TheTosters/TRNG-Ring-Oscilator/host_tools/results_90kHz.txt

Opening file: 'outputA.bin'
Loaded 8388608 samples of 2 distinct 1-bit-wide symbols

Running non-IID tests...

Running Most Common Value Estimate...
Literal MCV Estimate: mode = 4298712, p-hat = 0.51244640350341797, p_u = 0.51289094014308934
	Most Common Value Estimate = 0.963276 / 1 bit(s)

Running Entropic Statistic Estimates (bit strings only)...
Literal Collision Estimate: X-bar = 2.3815616665635146, sigma-hat = 0.48576993337007718, p = 0.74403384845214471
	Collision Test Estimate = 0.426560 / 1 bit(s)
Literal Markov Estimate: P_0 = 0.48755359649658203, P_1 = 0.51244640350341797, P_0,0 = 0.56341348616529274, P_0,1 = 0.43658651383470726, P_1,0 = 0.4153788390569082, P_1,1 = 0.5846211609430918, p_max = 1.2668170204170376e-30
	Markov Test Estimate = 0.775911 / 1 bit(s)
Literal Compression Estimate: X-bar = 4.0969888509940864, sigma-hat = 1.2383501643392119, p = 0.36698478366929632
	Compression Test Estimate = 0.241035 / 1 bit(s)

Running Tuple Estimates...
Literal t-Tuple Estimate: t = 148, p-hat_max = 0.91971073380307244, p_u = 0.91995240590938887
Literal LRS Estimate: u = 149, v = 214, p-hat = 0.87358722201162486, p_u = 0.87388276508104323
	T-Tuple Test Estimate = 0.120369 / 1 bit(s)
	LRS Test Estimate = 0.194488 / 1 bit(s)

Running Predictor Estimates...
Literal MultiMCW Prediction Estimate: N = 8388545, Pglobal' = 0.51260666561552337 (C = 4296295) Plocal = 0.71283473804017683 (r = 57)
	Multi Most Common in Window (MultiMCW) Prediction Test Estimate = 0.488360 / 1 bit(s)
Literal Lag Prediction Estimate: N = 8388607, Pglobal' = 0.57471232292201824 (C = 4817347) Plocal = 0.91959446713649384 (r = 215)
	Lag Prediction Test Estimate = 0.120930 / 1 bit(s)
Literal MultiMMC Prediction Estimate: N = 8388606, Pglobal' = 0.8222529756850907 (C = 6894702) Plocal = 0.91997141567862839 (r = 216)
	Multi Markov Model with Counting (MultiMMC) Prediction Test Estimate = 0.120339 / 1 bit(s)
Literal LZ78Y Prediction Estimate: N = 8388591, Pglobal' = 0.57471866305392549 (C = 4817391) Plocal = 0.91997142372295304 (r = 216)
	LZ78Y Prediction Test Estimate = 0.120339 / 1 bit(s)

H_original: 0.120339
Opening file: 'outputB.bin'
Loaded 8388608 samples of 2 distinct 1-bit-wide symbols

Running non-IID tests...

Running Most Common Value Estimate...
Literal MCV Estimate: mode = 4230372, p-hat = 0.50429964065551758, p_u = 0.50474429864658732
	Most Common Value Estimate = 0.986375 / 1 bit(s)

Running Entropic Statistic Estimates (bit strings only)...
Literal Collision Estimate: X-bar = 2.173933144739038, sigma-hat = 0.3790520322270397, p = 0.90408161203077464
	Collision Test Estimate = 0.145475 / 1 bit(s)
Literal Markov Estimate: P_0 = 0.49570035934448242, P_1 = 0.50429964065551758, P_0,0 = 0.8178407863334356, P_0,1 = 0.1821592136665644, P_1,0 = 0.17905309014268489, P_1,1 = 0.82094690985731511, p_max = 6.617635792806642e-12
	Markov Test Estimate = 0.290131 / 1 bit(s)
Literal Compression Estimate: X-bar = 3.4138333141020731, sigma-hat = 1.375676444584367, p = 0.50823522161718859
	Compression Test Estimate = 0.162739 / 1 bit(s)

Running Tuple Estimates...
Literal t-Tuple Estimate: t = 150, p-hat_max = 0.92248832676736736, p_u = 0.92272614007370446
Literal LRS Estimate: u = 151, v = 187, p-hat = 0.85635492738619756, p_u = 0.85666684824822803
	T-Tuple Test Estimate = 0.116026 / 1 bit(s)
	LRS Test Estimate = 0.223194 / 1 bit(s)

Running Predictor Estimates...
Literal MultiMCW Prediction Estimate: N = 8388545, Pglobal' = 0.51750655364266596 (C = 4337399) Plocal = 0.8975639045458621 (r = 169)
	Multi Most Common in Window (MultiMCW) Prediction Test Estimate = 0.155913 / 1 bit(s)
Literal Lag Prediction Estimate: N = 8388607, Pglobal' = 0.81974931825735786 (C = 6873685) Plocal = 0.89695502392683157 (r = 168)
	Lag Prediction Test Estimate = 0.156892 / 1 bit(s)
Literal MultiMMC Prediction Estimate: N = 8388606, Pglobal' = 0.83215606509176343 (C = 6977839) Plocal = 0.89695502459785259 (r = 168)
	Multi Markov Model with Counting (MultiMMC) Prediction Test Estimate = 0.156892 / 1 bit(s)
Literal LZ78Y Prediction Estimate: N = 8388591, Pglobal' = 0.81974945086986895 (C = 6873673) Plocal = 0.89695503466686577 (r = 168)
	LZ78Y Prediction Test Estimate = 0.156892 / 1 bit(s)

H_original: 0.116026
Opening file: 'outputC.bin'
Loaded 8388608 samples of 2 distinct 1-bit-wide symbols

Running non-IID tests...

Running Most Common Value Estimate...
Literal MCV Estimate: mode = 4272873, p-hat = 0.50936615467071533, p_u = 0.50981075107855722
	Most Common Value Estimate = 0.971966 / 1 bit(s)

Running Entropic Statistic Estimates (bit strings only)...
Literal Collision Estimate: X-bar = 2.4836991649062239, sigma-hat = 0.49973428611273651, p = 0.59219885774090075
	Collision Test Estimate = 0.755846 / 1 bit(s)
Literal Markov Estimate: P_0 = 0.49063384532928467, P_1 = 0.50936615467071533, P_0,0 = 0.44018345208898341, P_0,1 = 0.55981654791101665, P_1,0 = 0.53922899182821493, P_1,1 = 0.46077100817178507, p_max = 4.6494135477684564e-34
	Markov Test Estimate = 0.865066 / 1 bit(s)
Literal Compression Estimate: X-bar = 4.1554362921222205, sigma-hat = 1.2654374991161359, p = 0.35391090490677524
	Compression Test Estimate = 0.249757 / 1 bit(s)

Running Tuple Estimates...
Literal t-Tuple Estimate: t = 82, p-hat_max = 0.86038147790838959, p_u = 0.86068971805304306
Literal LRS Estimate: u = 83, v = 119, p-hat = 0.77715304576111677, p_u = 0.77752315402597705
	T-Tuple Test Estimate = 0.216435 / 1 bit(s)
	LRS Test Estimate = 0.363042 / 1 bit(s)

Running Predictor Estimates...
Literal MultiMCW Prediction Estimate: N = 8388545, Pglobal' = 0.50922604696704044 (C = 4267936) Plocal can't affect result (r = 13)
	Multi Most Common in Window (MultiMCW) Prediction Test Estimate = 0.973622 / 1 bit(s)
Literal Lag Prediction Estimate: N = 8388607, Pglobal' = 0.58395104214111504 (C = 4894858) Plocal = 0.83661674891755911 (r = 105)
	Lag Prediction Test Estimate = 0.257361 / 1 bit(s)
Literal MultiMMC Prediction Estimate: N = 8388606, Pglobal' = 0.82287085094884427 (C = 6899889) Plocal = 0.83955329877997165 (r = 107)
	Multi Markov Model with Counting (MultiMMC) Prediction Test Estimate = 0.252306 / 1 bit(s)
Literal LZ78Y Prediction Estimate: N = 8388591, Pglobal' = 0.54976741631726744 (C = 4608062) Plocal can't affect result (r = 16)
	LZ78Y Prediction Test Estimate = 0.863107 / 1 bit(s)

H_original: 0.216435
Opening file: 'outputD.bin'
Loaded 8388608 samples of 2 distinct 1-bit-wide symbols

Running non-IID tests...

Running Most Common Value Estimate...
Literal MCV Estimate: mode = 4335821, p-hat = 0.51687014102935791, p_u = 0.51731456227980532
	Most Common Value Estimate = 0.950886 / 1 bit(s)

Running Entropic Statistic Estimates (bit strings only)...
Literal Collision Estimate: X-bar = 2.2929617626863648, sigma-hat = 0.45512111015518786, p = 0.82221976076494396
	Collision Test Estimate = 0.282404 / 1 bit(s)
Literal Markov Estimate: P_0 = 0.48312985897064209, P_1 = 0.51687014102935791, P_0,0 = 0.71552235918698892, P_0,1 = 0.28447764081301108, P_1,0 = 0.26590765624318902, P_1,1 = 0.73409234375681098, p_max = 4.6101988602429338e-18
	Markov Test Estimate = 0.449921 / 1 bit(s)
Literal Compression Estimate: X-bar = 4.0684669349208216, sigma-hat = 1.1736546335303886, p = 0.37327169556855921
	Compression Test Estimate = 0.236950 / 1 bit(s)

Running Tuple Estimates...
Literal t-Tuple Estimate: t = 91, p-hat_max = 0.87300709263041121, p_u = 0.87330321469890448
Literal LRS Estimate: u = 92, v = 111, p-hat = 0.77085064704799344, p_u = 0.77122442750751286
	T-Tuple Test Estimate = 0.195445 / 1 bit(s)
	LRS Test Estimate = 0.374777 / 1 bit(s)

Running Predictor Estimates...
Literal MultiMCW Prediction Estimate: N = 8388545, Pglobal' = 0.51703962133377257 (C = 4333482) Plocal = 0.8366168108271288 (r = 105)
	Multi Most Common in Window (MultiMCW) Prediction Test Estimate = 0.257361 / 1 bit(s)
Literal Lag Prediction Estimate: N = 8388607, Pglobal' = 0.72551768378603787 (C = 6082752) Plocal = 0.84646646661947711 (r = 112)
	Lag Prediction Test Estimate = 0.240475 / 1 bit(s)
Literal MultiMMC Prediction Estimate: N = 8388606, Pglobal' = 0.80895859134096559 (C = 6783100) Plocal = 0.83042085935645926 (r = 101)
	Multi Markov Model with Counting (MultiMMC) Prediction Test Estimate = 0.268085 / 1 bit(s)
Literal LZ78Y Prediction Estimate: N = 8388591, Pglobal' = 0.72551751757617944 (C = 6082739) Plocal = 0.84646648178079575 (r = 112)
	LZ78Y Prediction Test Estimate = 0.240475 / 1 bit(s)

H_original: 0.195445
Opening file: 'outputE.bin'
Loaded 8388608 samples of 2 distinct 1-bit-wide symbols

Running non-IID tests...

Running Most Common Value Estimate...
Literal MCV Estimate: mode = 4305989, p-hat = 0.513313889503479, p_u = 0.51375840626253888
	Most Common Value Estimate = 0.960838 / 1 bit(s)

Running Entropic Statistic Estimates (bit strings only)...
Literal Collision Estimate: X-bar = 2.609804851247532, sigma-hat = 0.48779398178909766, p = 0.5
	Collision Test Estimate = 1.000000 / 1 bit(s)
Literal Markov Estimate: P_0 = 0.486686110496521, P_1 = 0.513313889503479, P_0,0 = 0.35408039645149264, P_0,1 = 0.6459196035485073, P_1,0 = 0.61241308326612076, P_1,1 = 0.38758691673387924, p_max = 1.3257810065688544e-26
	Markov Test Estimate = 0.671588 / 1 bit(s)
Literal Compression Estimate: X-bar = 4.1545489860127169, sigma-hat = 1.2084756619072359, p = 0.35408303695351973
	Compression Test Estimate = 0.249640 / 1 bit(s)

Running Tuple Estimates...
Literal t-Tuple Estimate: t = 76, p-hat_max = 0.85022349373191985, p_u = 0.85054085984579109
Literal LRS Estimate: u = 77, v = 108, p-hat = 0.75469758505810292, p_u = 0.75508024195678169
	T-Tuple Test Estimate = 0.233548 / 1 bit(s)
	LRS Test Estimate = 0.405298 / 1 bit(s)

Running Predictor Estimates...
Literal MultiMCW Prediction Estimate: N = 8388545, Pglobal' = 0.513408813018286 (C = 4303024) Plocal can't affect result (r = 12)
	Multi Most Common in Window (MultiMCW) Prediction Test Estimate = 0.961820 / 1 bit(s)
Literal Lag Prediction Estimate: N = 8388607, Pglobal' = 0.62968135364052824 (C = 5278546) Plocal = 0.70371374522201624 (r = 55)
	Lag Prediction Test Estimate = 0.506939 / 1 bit(s)
Literal MultiMMC Prediction Estimate: N = 8388606, Pglobal' = 0.81340886948187918 (C = 6820458) Plocal = 0.83809789327235407 (r = 106)
	Multi Markov Model with Counting (MultiMMC) Prediction Test Estimate = 0.254809 / 1 bit(s)
Literal LZ78Y Prediction Estimate: N = 8388591, Pglobal' = 0.62914945635925423 (C = 5274073) Plocal = 0.80251477315347142 (r = 86)
	LZ78Y Prediction Test Estimate = 0.317400 / 1 bit(s)

H_original: 0.233548
Opening file: 'outputF.bin'
Loaded 8388608 samples of 2 distinct 1-bit-wide symbols

Running non-IID tests...

Running Most Common Value Estimate...
Literal MCV Estimate: mode = 4260564, p-hat = 0.50789880752563477, p_u = 0.50834342646735065
	Most Common Value Estimate = 0.976125 / 1 bit(s)

Running Entropic Statistic Estimates (bit strings only)...
Literal Collision Estimate: X-bar = 2.7115709227400528, sigma-hat = 0.45303179909682284, p = 0.5
	Collision Test Estimate = 1.000000 / 1 bit(s)
Literal Markov Estimate: P_0 = 0.49210119247436523, P_1 = 0.50789880752563477, P_0,0 = 0.2674266553360381, P_0,1 = 0.73257334466396196, P_1,0 = 0.70978765012980682, P_1,1 = 0.29021234987019318, p_max = 4.6091129125894903e-19
	Markov Test Estimate = 0.475876 / 1 bit(s)
Literal Compression Estimate: X-bar = 3.9043233688137411, sigma-hat = 1.2903146020321519, p = 0.40887981166314613
	Compression Test Estimate = 0.215042 / 1 bit(s)

Running Tuple Estimates...
Literal t-Tuple Estimate: t = 138, p-hat_max = 0.91414962264868693, p_u = 0.91439876749138815
Literal LRS Estimate: u = 139, v = 173, p-hat = 0.84102190629608664, p_u = 0.84134710173967131
	T-Tuple Test Estimate = 0.129105 / 1 bit(s)
	LRS Test Estimate = 0.249227 / 1 bit(s)

Running Predictor Estimates...
Literal MultiMCW Prediction Estimate: N = 8388545, Pglobal' = 0.50708398853688175 (C = 4249967) Plocal can't affect result (r = 13)
	Multi Most Common in Window (MultiMCW) Prediction Test Estimate = 0.979703 / 1 bit(s)
Literal Lag Prediction Estimate: N = 8388607, Pglobal' = 0.53158253313116521 (C = 4455514) Plocal = 0.80464711951090206 (r = 87)
	Lag Prediction Test Estimate = 0.313572 / 1 bit(s)
Literal MultiMMC Prediction Estimate: N = 8388606, Pglobal' = 0.80132154710984138 (C = 6718992) Plocal = 0.89380262309515446 (r = 163)
	Multi Markov Model with Counting (MultiMMC) Prediction Test Estimate = 0.161972 / 1 bit(s)
Literal LZ78Y Prediction Estimate: N = 8388591, Pglobal' = 0.72139886683620547 (C = 6048174) Plocal = 0.89181998752301628 (r = 160)
	LZ78Y Prediction Test Estimate = 0.165176 / 1 bit(s)

H_original: 0.129105
Opening file: 'outputA-F.bin'
Loaded 1398101 samples of 64 distinct 6-bit-wide symbols
Number of Binary Symbols: 8388606

Running non-IID tests...

Running Most Common Value Estimate...
Bitstring MCV Estimate: mode = 4279520, p-hat = 0.51015866044966229, p_u = 0.51060324314650907
	Most Common Value Estimate (bit string) = 0.969725 / 1 bit(s)
Literal MCV Estimate: mode = 30234, p-hat = 0.021625047117482928, p_u = 0.021941915681613411
	Most Common Value Estimate = 5.510167 / 6 bit(s)

Running Entropic Statistic Estimates (bit strings only)...
Bitstring Collision Estimate: X-bar = 2.4942242713215821, sigma-hat = 0.49996671417409239, p = 0.55691204344919609
	Collision Test Estimate (bit string) = 0.844479 / 1 bit(s)
Bitstring Markov Estimate: P_0 = 0.48984133955033771, P_1 = 0.51015866044966229, P_0,0 = 0.49528520339686327, P_0,1 = 0.50471479660313667, P_1,0 = 0.48461439600702882, P_1,1 = 0.51538560399297118, p_max = 1.4076842853261408e-37
	Markov Test Estimate (bit string) = 0.956391 / 1 bit(s)
Bitstring Compression Estimate: X-bar = 5.1839970913330653, sigma-hat = 1.0208165534184075, p = 0.05185236007780869
	Compression Test Estimate (bit string) = 0.711574 / 1 bit(s)

Running Tuple Estimates...
Bitstring t-Tuple Estimate: t = 28, p-hat_max = 0.6492966990368092, p_u = 0.64972108765842607
Bitstring LRS Estimate: u = 29, v = 90, p-hat = 0.71451064879251669, p_u = 0.71491232075373568
	T-Tuple Test Estimate (bit string) = 0.622108 / 1 bit(s)
Literal t-Tuple Estimate: t = 4, p-hat_max = 0.08288989323938957, p_u = 0.083490526657149858
Literal LRS Estimate: u = 5, v = 14, p-hat = 0.14624155830546209, p_u = 0.14701131038388546
	T-Tuple Test Estimate = 3.582244 / 6 bit(s)
	LRS Test Estimate (bit string) = 0.484162 / 1 bit(s)
	LRS Test Estimate = 2.766001 / 6 bit(s)

Running Predictor Estimates...
Bitstring MultiMCW Prediction Estimate: N = 8388543, Pglobal' = 0.50994773600696053 (C = 4273989) Plocal can't affect result (r = 19)
	Multi Most Common in Window (MultiMCW) Prediction Test Estimate (bit string) = 0.971579 / 1 bit(s)
Literal MultiMCW Prediction Estimate: N = 1398038, Pglobal' = 0.020720229688916007 (C = 28537) Plocal can't affect result (r = 4)
	Multi Most Common in Window (MultiMCW) Prediction Test Estimate = 5.592816 / 6 bit(s)
Bitstring Lag Prediction Estimate: N = 8388605, Pglobal' = 0.53051782092749111 (C = 4446581) Plocal can't affect result (r = 23)
	Lag Prediction Test Estimate (bit string) = 0.914527 / 1 bit(s)
Literal Lag Prediction Estimate: N = 1398100, Pglobal' = 0.024532587396390054 (C = 33831) Plocal can't affect result (r = 5)
	Lag Prediction Test Estimate = 5.349157 / 6 bit(s)
Bitstring MultiMMC Prediction Estimate: N = 8388604, Pglobal' = 0.61223139835262042 (C = 5132131) Plocal can't affect result (r = 34)
	Multi Markov Model with Counting (MultiMMC) Prediction Test Estimate (bit string) = 0.707851 / 1 bit(s)
Literal MultiMMC Prediction Estimate: N = 1398099, Pglobal' = 0.11453364169286714 (C = 159162) Plocal can't affect result (r = 8)
	Multi Markov Model with Counting (MultiMMC) Prediction Test Estimate = 3.126157 / 6 bit(s)
Bitstring LZ78Y Prediction Estimate: N = 8388589, Pglobal' = 0.51056958809083852 (C = 4279229) Plocal can't affect result (r = 19)
	LZ78Y Prediction Test Estimate (bit string) = 0.969820 / 1 bit(s)
Literal LZ78Y Prediction Estimate: N = 1398084, Pglobal' = 0.054053795111667954 (C = 74886) Plocal can't affect result (r = 4)
	LZ78Y Prediction Test Estimate = 4.209460 / 6 bit(s)

H_original: 2.766001
H_bitstring: 0.484162
min(H_original, 6 X H_bitstring): 2.766001
