TheTosters/TRNG-Ring-Oscilator/host_tools/Rev_2/sweep/300kHz/results.txt

########## channel A (1 bit/sample, little) ##########
Opening file: 'Rev_2/sweep/300kHz/outputA.bin'
Loaded 4194304 samples of 2 distinct 1-bit-wide symbols

Running non-IID tests...

Running Most Common Value Estimate...
Literal MCV Estimate: mode = 2104973, p-hat = 0.50186467170715332, p_u = 0.50249353198504088
	Most Common Value Estimate = 0.992823 / 1 bit(s)

Running Entropic Statistic Estimates (bit strings only)...
Literal Collision Estimate: X-bar = 2.4009455401393751, sigma-hat = 0.49009014627186415, p = 0.72361749916627005
	Collision Test Estimate = 0.466701 / 1 bit(s)
Literal Markov Estimate: P_0 = 0.49813532829284668, P_1 = 0.50186467170715332, P_0,0 = 0.58695945590213128, P_0,1 = 0.41304054409786872, P_1,0 = 0.40997105426055347, P_1,1 = 0.59002894573944653, p_max = 3.9948271499480619e-30
	Markov Test Estimate = 0.762966 / 1 bit(s)
Literal Compression Estimate: X-bar = 4.8000140811946661, sigma-hat = 1.1849010690096364, p = 0.19228632566695947
	Compression Test Estimate = 0.396445 / 1 bit(s)

Running Tuple Estimates...
Literal t-Tuple Estimate: t = 35, p-hat_max = 0.71711203262643819, p_u = 0.71767851698317953
Literal LRS Estimate: u = 36, v = 52, p-hat = 0.57241842177660929, p_u = 0.57304065539682425
	T-Tuple Test Estimate = 0.478590 / 1 bit(s)
	LRS Test Estimate = 0.803291 / 1 bit(s)

Running Predictor Estimates...
Literal MultiMCW Prediction Estimate: N = 4194241, Pglobal' = 0.49990346928946011 (C = 2094078) Plocal = 0.68272672936166467 (r = 49)
	Multi Most Common in Window (MultiMCW) Prediction Test Estimate = 0.550620 / 1 bit(s)
Literal Lag Prediction Estimate: N = 4194303, Pglobal' = 0.58911862191860864 (C = 2468346) Plocal = 0.67707018882865655 (r = 48)
	Lag Prediction Test Estimate = 0.562623 / 1 bit(s)
Literal MultiMMC Prediction Estimate: N = 4194302, Pglobal' = 0.63641327884093557 (C = 2666771) Plocal = 0.67707019234508858 (r = 48)
	Multi Markov Model with Counting (MultiMMC) Prediction Test Estimate = 0.562623 / 1 bit(s)
Literal LZ78Y Prediction Estimate: N = 4194287, Pglobal' = 0.58911824552680403 (C = 2468335) Plocal = 0.67707024509547686 (r = 48)
	LZ78Y Prediction Test Estimate = 0.562623 / 1 bit(s)

H_original: 0.396445

########## channel B (1 bit/sample, little) ##########
Opening file: 'Rev_2/sweep/300kHz/outputB.bin'
Loaded 4194304 samples of 2 distinct 1-bit-wide symbols

Running non-IID tests...

Running Most Common Value Estimate...
Literal MCV Estimate: mode = 2149442, p-hat = 0.5124669075012207, p_u = 0.5130955766408114
	Most Common Value Estimate = 0.962701 / 1 bit(s)

Running Entropic Statistic Estimates (bit strings only)...
Literal Collision Estimate: X-bar = 2.3396478063621107, sigma-hat = 0.47358980046711291, p = 0.78395711907345444
	Collision Test Estimate = 0.351153 / 1 bit(s)
Literal Markov Estimate: P_0 = 0.4875330924987793, P_1 = 0.5124669075012207, P_0,0 = 0.65388014148638951, P_0,1 = 0.34611985851361049, P_1,0 = 0.32927941298253222, P_1,1 = 0.67072058701746773, p_max = 4.7913035985386578e-23
	Markov Test Estimate = 0.579249 / 1 bit(s)
Literal Compression Estimate: X-bar = 4.7130704313544349, sigma-hat = 1.2276205430137941, p = 0.21676812413000471
	Compression Test Estimate = 0.367629 / 1 bit(s)

Running Tuple Estimates...
Literal t-Tuple Estimate: t = 44, p-hat_max = 0.7675842442246763, p_u = 0.76811547470794417
Literal LRS Estimate: u = 45, v = 63, p-hat = 0.63119868239556165, p_u = 0.63180551157100495
	T-Tuple Test Estimate = 0.380605 / 1 bit(s)
	LRS Test Estimate = 0.662448 / 1 bit(s)

Running Predictor Estimates...
Literal MultiMCW Prediction Estimate: N = 4194241, Pglobal' = 0.51098328971911711 (C = 2140550) Plocal = 0.7083906066829706 (r = 54)
	Multi Most Common in Window (MultiMCW) Prediction Test Estimate = 0.497383 / 1 bit(s)
Literal Lag Prediction Estimate: N = 4194303, Pglobal' = 0.66310455968221371 (C = 2778767) Plocal = 0.74208279285977319 (r = 62)
	Lag Prediction Test Estimate = 0.430348 / 1 bit(s)
Literal MultiMMC Prediction Estimate: N = 4194302, Pglobal' = 0.66374912249817097 (C = 2781471) Plocal = 0.7420827958526679 (r = 62)
	Multi Markov Model with Counting (MultiMMC) Prediction Test Estimate = 0.430348 / 1 bit(s)
Literal LZ78Y Prediction Estimate: N = 4194287, Pglobal' = 0.66310446552747671 (C = 2778756) Plocal = 0.74208284074089403 (r = 62)
	LZ78Y Prediction Test Estimate = 0.430348 / 1 bit(s)

H_original: 0.351153

########## channel C (1 bit/sample, little) ##########
Opening file: 'Rev_2/sweep/300kHz/outputC.bin'
Loaded 4194304 samples of 2 distinct 1-bit-wide symbols

Running non-IID tests...

Running Most Common Value Estimate...
Literal MCV Estimate: mode = 2135096, p-hat = 0.50904655456542969, p_u = 0.5096753162752784
	Most Common Value Estimate = 0.972350 / 1 bit(s)

Running Entropic Statistic Estimates (bit strings only)...
Literal Collision Estimate: X-bar = 2.5236926516768343, sigma-hat = 0.4994384930526059, p = 0.5
	Collision Test Estimate = 1.000000 / 1 bit(s)
Literal Markov Estimate: P_0 = 0.49095344543457031, P_1 = 0.50904655456542969, P_0,0 = 0.45386063664313497, P_0,1 = 0.54613936335686497, P_1,0 = 0.52672760381734596, P_1,1 = 0.47327239618265404, p_max = 2.179646039319764e-35
	Markov Test Estimate = 0.899558 / 1 bit(s)
Literal Compression Estimate: X-bar = 4.834841144327866, sigma-hat = 1.1700264995820584, p = 0.18211362950822052
	Compression Test Estimate = 0.409515 / 1 bit(s)

Running Tuple Estimates...
Literal t-Tuple Estimate: t = 30, p-hat_max = 0.67783114505111675, p_u = 0.67841889109665721
Literal LRS Estimate: u = 31, v = 50, p-hat = 0.56261013677922722, p_u = 0.56323405161454465
	T-Tuple Test Estimate = 0.559752 / 1 bit(s)
	LRS Test Estimate = 0.828194 / 1 bit(s)

Running Predictor Estimates...
Literal MultiMCW Prediction Estimate: N = 4194241, Pglobal' = 0.50752195189640548 (C = 2126032) Plocal = 0.59945055608291298 (r = 37)
	Multi Most Common in Window (MultiMCW) Prediction Test Estimate = 0.738287 / 1 bit(s)
Literal Lag Prediction Estimate: N = 4194303, Pglobal' = 0.51779332453569549 (C = 2169146) Plocal = 0.65889174011725271 (r = 45)
	Lag Prediction Test Estimate = 0.601887 / 1 bit(s)
Literal MultiMMC Prediction Estimate: N = 4194302, Pglobal' = 0.63116107227105633 (C = 2644734) Plocal = 0.67707019234508858 (r = 48)
	Multi Markov Model with Counting (MultiMMC) Prediction Test Estimate = 0.562623 / 1 bit(s)
Literal LZ78Y Prediction Estimate: N = 4194287, Pglobal' = 0.53687568437009525 (C = 2249180) Plocal = 0.67707024509547686 (r = 48)
	LZ78Y Prediction Test Estimate = 0.562623 / 1 bit(s)

H_original: 0.409515

########## channel D (1 bit/sample, little) ##########
Opening file: 'Rev_2/sweep/300kHz/outputD.bin'
Loaded 4194304 samples of 2 distinct 1-bit-wide symbols

Running non-IID tests...

Running Most Common Value Estimate...
Literal MCV Estimate: mode = 2140860, p-hat = 0.51042079925537109, p_u = 0.51104952731089448
	Most Common Value Estimate = 0.968465 / 1 bit(s)

Running Entropic Statistic Estimates (bit strings only)...
Literal Collision Estimate: X-bar = 2.6637943298445279, sigma-hat = 0.47241037165435557, p = 0.5
	Collision Test Estimate = 1.000000 / 1 bit(s)
Literal Markov Estimate: P_0 = 0.48957920074462891, P_1 = 0.51042079925537109, P_0,0 = 0.32409405856697332, P_0,1 = 0.67590594143302662, P_1,0 = 0.6483070580547341, P_1,1 = 0.3516929419452659, p_max = 8.8050351173577593e-24
	Markov Test Estimate = 0.598343 / 1 bit(s)
Literal Compression Estimate: X-bar = 4.7414444428009972, sigma-hat = 1.2232078300470093, p = 0.20891815025471139
	Compression Test Estimate = 0.376498 / 1 bit(s)

Running Tuple Estimates...
Literal t-Tuple Estimate: t = 36, p-hat_max = 0.72545950049844177, p_u = 0.72602080299653482
Literal LRS Estimate: u = 37, v = 56, p-hat = 0.60601644543564825, p_u = 0.60663101129574781
	T-Tuple Test Estimate = 0.461917 / 1 bit(s)
	LRS Test Estimate = 0.721109 / 1 bit(s)

Running Predictor Estimates...
Literal MultiMCW Prediction Estimate: N = 4194241, Pglobal' = 0.5092924402117176 (C = 2133458) Plocal can't affect result (r = 17)
	Multi Most Common in Window (MultiMCW) Prediction Test Estimate = 0.973434 / 1 bit(s)
Literal Lag Prediction Estimate: N = 4194303, Pglobal' = 0.57999534157353749 (C = 2430072) Plocal = 0.7219652006235483 (r = 57)
	Lag Prediction Test Estimate = 0.469999 / 1 bit(s)
Literal MultiMMC Prediction Estimate: N = 4194302, Pglobal' = 0.66251655413784383 (C = 2776299) Plocal = 0.72622510066901247 (r = 58)
	Multi Markov Model with Counting (MultiMMC) Prediction Test Estimate = 0.461511 / 1 bit(s)
Literal LZ78Y Prediction Estimate: N = 4194287, Pglobal' = 0.66241287036999663 (C = 2775854) Plocal = 0.72622514759518997 (r = 58)
	LZ78Y Prediction Test Estimate = 0.461511 / 1 bit(s)

H_original: 0.376498

########## channel E (1 bit/sample, little) ##########
Opening file: 'Rev_2/sweep/300kHz/outputE.bin'
Loaded 4194304 samples of 2 distinct 1-bit-wide symbols

Running non-IID tests...

Running Most Common Value Estimate...
Literal MCV Estimate: mode = 2110117, p-hat = 0.50309109687805176, p_u = 0.50371994951151278
	Most Common Value Estimate = 0.989306 / 1 bit(s)

Running Entropic Statistic Estimates (bit strings only)...
Literal Collision Estimate: X-bar = 2.3443902204539651, sigma-hat = 0.47516915168358986, p = 0.77975421454803273
	Collision Test Estimate = 0.358909 / 1 bit(s)
Literal Markov Estimate: P_0 = 0.49690890312194824, P_1 = 0.50309109687805176, P_0,0 = 0.65248063272663759, P_0,1 = 0.34751936727336241, P_1,0 = 0.34324921319528728, P_1,1 = 0.65675078680471266, p_max = 3.2473048007993448e-24
	Markov Test Estimate = 0.609586 / 1 bit(s)
Literal Compression Estimate: X-bar = 4.7018737406979012, sigma-hat = 1.2244399261081302, p = 0.21982968148533172
	Compression Test Estimate = 0.364257 / 1 bit(s)

Running Tuple Estimates...
Literal t-Tuple Estimate: t = 44, p-hat_max = 0.76850316884669401, p_u = 0.76903366536218165
Literal LRS Estimate: u = 45, v = 63, p-hat = 0.63423235845356107, p_u = 0.63483813718023108
	T-Tuple Test Estimate = 0.378881 / 1 bit(s)
	LRS Test Estimate = 0.655539 / 1 bit(s)

Running Predictor Estimates...
Literal MultiMCW Prediction Estimate: N = 4194241, Pglobal' = 0.50583084924175137 (C = 2118939) Plocal = 0.73438064201989661 (r = 60)
	Multi Most Common in Window (MultiMCW) Prediction Test Estimate = 0.445400 / 1 bit(s)
Literal Lag Prediction Estimate: N = 4194303, Pglobal' = 0.6552259931197274 (C = 2745708) Plocal = 0.74936803417853515 (r = 64)
	Lag Prediction Test Estimate = 0.416254 / 1 bit(s)
Literal MultiMMC Prediction Estimate: N = 4194302, Pglobal' = 0.65917772972033162 (C = 2762289) Plocal = 0.74936803710731892 (r = 64)
	Multi Markov Model with Counting (MultiMMC) Prediction Test Estimate = 0.416254 / 1 bit(s)
Literal LZ78Y Prediction Estimate: N = 4194287, Pglobal' = 0.65522729884645348 (C = 2745703) Plocal = 0.74936808103399155 (r = 64)
	LZ78Y Prediction Test Estimate = 0.416254 / 1 bit(s)

H_original: 0.358909

########## channel F (1 bit/sample, little) ##########
Opening file: 'Rev_2/sweep/300kHz/outputF.bin'
Loaded 4194304 samples of 2 distinct 1-bit-wide symbols

Running non-IID tests...

Running Most Common Value Estimate...
Literal MCV Estimate: mode = 2186627, p-hat = 0.5213325023651123, p_u = 0.52196079439344656
	Most Common Value Estimate = 0.937987 / 1 bit(s)

Running Entropic Statistic Estimates (bit strings only)...
Literal Collision Estimate: X-bar = 2.6755490092763528, sigma-hat = 0.46816950472973917, p = 0.5
	Collision Test Estimate = 1.000000 / 1 bit(s)
Literal Markov Estimate: P_0 = 0.4786674976348877, P_1 = 0.5213325023651123, P_0,0 = 0.29387909204473234, P_0,1 = 0.70612090795526772, P_1,0 = 0.64833279750044248, P_1,1 = 0.35166720249955752, p_max = 1.417646590214333e-22
	Markov Test Estimate = 0.567023 / 1 bit(s)
Literal Compression Estimate: X-bar = 4.6660745243763895, sigma-hat = 1.2510538149355399, p = 0.22953504411320583
	Compression Test Estimate = 0.353869 / 1 bit(s)

Running Tuple Estimates...
Literal t-Tuple Estimate: t = 41, p-hat_max = 0.75430405880002771, p_u = 0.75484551008962619
Literal LRS Estimate: u = 42, v = 58, p-hat = 0.61684472876018948, p_u = 0.61745618095793209
	T-Tuple Test Estimate = 0.405747 / 1 bit(s)
	LRS Test Estimate = 0.695591 / 1 bit(s)

Running Predictor Estimates...
Literal MultiMCW Prediction Estimate: N = 4194241, Pglobal' = 0.52144532054805992 (C = 2184432) Plocal can't affect result (r = 18)
	Multi Most Common in Window (MultiMCW) Prediction Test Estimate = 0.939412 / 1 bit(s)
Literal Lag Prediction Estimate: N = 4194303, Pglobal' = 0.60452167273537072 (C = 2532967) Plocal = 0.72622509754087183 (r = 58)
	Lag Prediction Test Estimate = 0.461511 / 1 bit(s)
Literal MultiMMC Prediction Estimate: N = 4194302, Pglobal' = 0.67658214697122576 (C = 2835321) Plocal = 0.73036180461747902 (r = 59)
	Multi Markov Model with Counting (MultiMMC) Prediction Test Estimate = 0.453317 / 1 bit(s)
Literal LZ78Y Prediction Estimate: N = 4194287, Pglobal' = 0.67658170475001456 (C = 2835309) Plocal = 0.73036185101896012 (r = 59)
	LZ78Y Prediction Test Estimate = 0.453317 / 1 bit(s)

H_original: 0.353869

########## channel G (1 bit/sample, little) ##########
Opening file: 'Rev_2/sweep/300kHz/outputG.bin'
Loaded 4194304 samples of 2 distinct 1-bit-wide symbols

Running non-IID tests...

Running Most Common Value Estimate...
Literal MCV Estimate: mode = 2146213, p-hat = 0.51169705390930176, p_u = 0.51232574645290985
	Most Common Value Estimate = 0.964867 / 1 bit(s)

Running Entropic Statistic Estimates (bit strings only)...
Literal Collision Estimate: X-bar = 2.4063907606778026, sigma-hat = 0.49115929057516139, p = 0.71744829241707075
	Collision Test Estimate = 0.479053 / 1 bit(s)
Literal Markov Estimate: P_0 = 0.48830294609069824, P_1 = 0.51169705390930176, P_0,0 = 0.58122641094873762, P_0,1 = 0.41877358905126238, P_1,0 = 0.399628089103924, P_1,1 = 0.600371910896076, p_max = 3.7016834769443604e-29
	Markov Test Estimate = 0.737873 / 1 bit(s)
Literal Compression Estimate: X-bar = 4.8643878273632941, sigma-hat = 1.1647840650344596, p = 0.17329691617628465
	Compression Test Estimate = 0.421447 / 1 bit(s)

Running Tuple Estimates...
Literal t-Tuple Estimate: t = 30, p-hat_max = 0.68339222106976472, p_u = 0.68397725760055172
Literal LRS Estimate: u = 31, v = 51, p-hat = 0.56897581795384833, p_u = 0.56959867000881403
	T-Tuple Test Estimate = 0.547980 / 1 bit(s)
	LRS Test Estimate = 0.811982 / 1 bit(s)

Running Predictor Estimates...
Literal MultiMCW Prediction Estimate: N = 4194241, Pglobal' = 0.51067001103879195 (C = 2139236) Plocal = 0.63141806302589543 (r = 41)
	Multi Most Common in Window (MultiMCW) Prediction Test Estimate = 0.663333 / 1 bit(s)
Literal Lag Prediction Estimate: N = 4194303, Pglobal' = 0.59164003540493004 (C = 2478924) Plocal = 0.6238858310914952 (r = 40)
	Lag Prediction Test Estimate = 0.680646 / 1 bit(s)
Literal MultiMMC Prediction Estimate: N = 4194302, Pglobal' = 0.62079538302636095 (C = 2601243) Plocal can't affect result (r = 39)
	Multi Markov Model with Counting (MultiMMC) Prediction Test Estimate = 0.687810 / 1 bit(s)
Literal LZ78Y Prediction Estimate: N = 4194287, Pglobal' = 0.59164086045311726 (C = 2478918) Plocal = 0.62388589316452214 (r = 40)
	LZ78Y Prediction Test Estimate = 0.680646 / 1 bit(s)

H_original: 0.421447

########## channel H (1 bit/sample, little) ##########
Opening file: 'Rev_2/sweep/300kHz/outputH.bin'
Loaded 4194304 samples of 2 distinct 1-bit-wide symbols

Running non-IID tests...

Running Most Common Value Estimate...
Literal MCV Estimate: mode = 2126513, p-hat = 0.50700020790100098, p_u = 0.50762901091661217
	Most Common Value Estimate = 0.978154 / 1 bit(s)

Running Entropic Statistic Estimates (bit strings only)...
Literal Collision Estimate: X-bar = 2.5163201027093183, sigma-hat = 0.49973373317423492, p = 0.5
	Collision Test Estimate = 1.000000 / 1 bit(s)
Literal Markov Estimate: P_0 = 0.50700020790100098, P_1 = 0.49299979209899902, P_0,0 = 0.47923102280587987, P_0,1 = 0.52076897719412019, P_1,0 = 0.53555776940598421, P_1,1 = 0.46444223059401579, p_max = 3.0555772463120925e-36
	Markov Test Estimate = 0.921703 / 1 bit(s)
Literal Compression Estimate: X-bar = 4.9343817179505312, sigma-hat = 1.1358907264075335, p = 0.1515584950324137
	Compression Test Estimate = 0.453676 / 1 bit(s)

Running Tuple Estimates...
Literal t-Tuple Estimate: t = 27, p-hat_max = 0.65109553681341392, p_u = 0.65169500039027239
Literal LRS Estimate: u = 28, v = 49, p-hat = 0.54985004457839826, p_u = 0.55047577593244867
	T-Tuple Test Estimate = 0.617731 / 1 bit(s)
	LRS Test Estimate = 0.861249 / 1 bit(s)

Running Predictor Estimates...
Literal MultiMCW Prediction Estimate: N = 4194241, Pglobal' = 0.5042637178009145 (C = 2112366) Plocal can't affect result (r = 26)
	Multi Most Common in Window (MultiMCW) Prediction Test Estimate = 0.987750 / 1 bit(s)
Literal Lag Prediction Estimate: N = 4194303, Pglobal' = 0.53133158747167319 (C = 2225933) Plocal = 0.55143004641925952 (r = 32)
	Lag Prediction Test Estimate = 0.858750 / 1 bit(s)
Literal MultiMMC Prediction Estimate: N = 4194302, Pglobal' = 0.61610187413474948 (C = 2581551) Plocal can't affect result (r = 34)
	Multi Markov Model with Counting (MultiMMC) Prediction Test Estimate = 0.698759 / 1 bit(s)
Literal LZ78Y Prediction Estimate: N = 4194287, Pglobal' = 0.52868711357999532 (C = 2214832) Plocal = 0.61605868555110821 (r = 39)
	LZ78Y Prediction Test Estimate = 0.698860 / 1 bit(s)

H_original: 0.453676
