TheTosters/TRNG-Ring-Oscilator/host_tools/Rev_1/100kHz/results.txt

########## channel A (1 bit/sample, little) ##########
Opening file: '100kHz/outputA.bin'
Loaded 8388608 samples of 2 distinct 1-bit-wide symbols

Running non-IID tests...

Running Most Common Value Estimate...
Literal MCV Estimate: mode = 4311527, p-hat = 0.51397407054901123, p_u = 0.51441857128048474
	Most Common Value Estimate = 0.958985 / 1 bit(s)

Running Entropic Statistic Estimates (bit strings only)...
Literal Collision Estimate: X-bar = 2.772305979888686, sigma-hat = 0.41934414438791207, p = 0.5
	Collision Test Estimate = 1.000000 / 1 bit(s)
Literal Markov Estimate: P_0 = 0.48602592945098877, P_1 = 0.51397407054901123, P_0,0 = 0.1970971872026058, P_0,1 = 0.80290281279739417, P_1,0 = 0.75924353483116302, P_1,1 = 0.24075646516883698, p_max = 1.1196945775157383e-14
	Markov Test Estimate = 0.362062 / 1 bit(s)
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
